linomp/acoustic-cam-usfq/development_version/postProc/16_mics_PSF.bmp

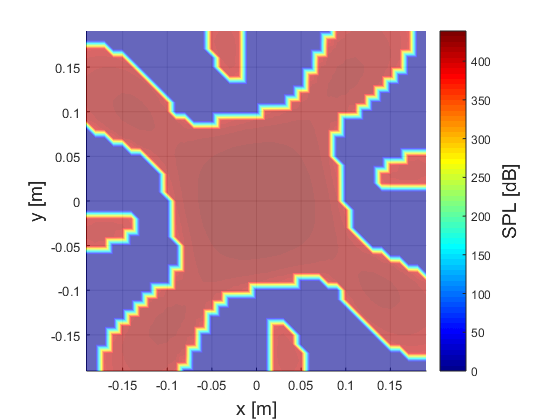
development_version/postProc/16_mics_PSF.bmp
