linomp/acoustic-cam-usfq/development_version/postProc/16_mics_PSF_w.bmp

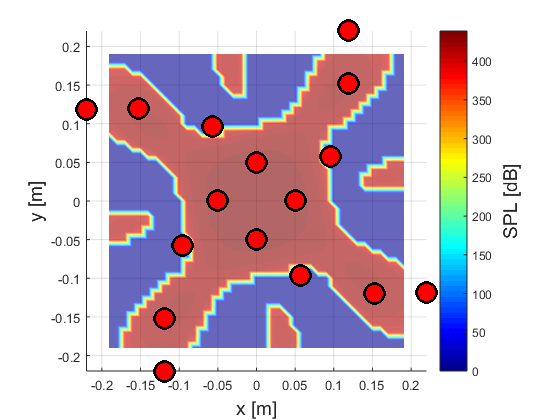
development_version/postProc/16_mics_PSF_w.bmp
