linomp/acoustic-cam-usfq/development_version/postProc/control_pt.bmp

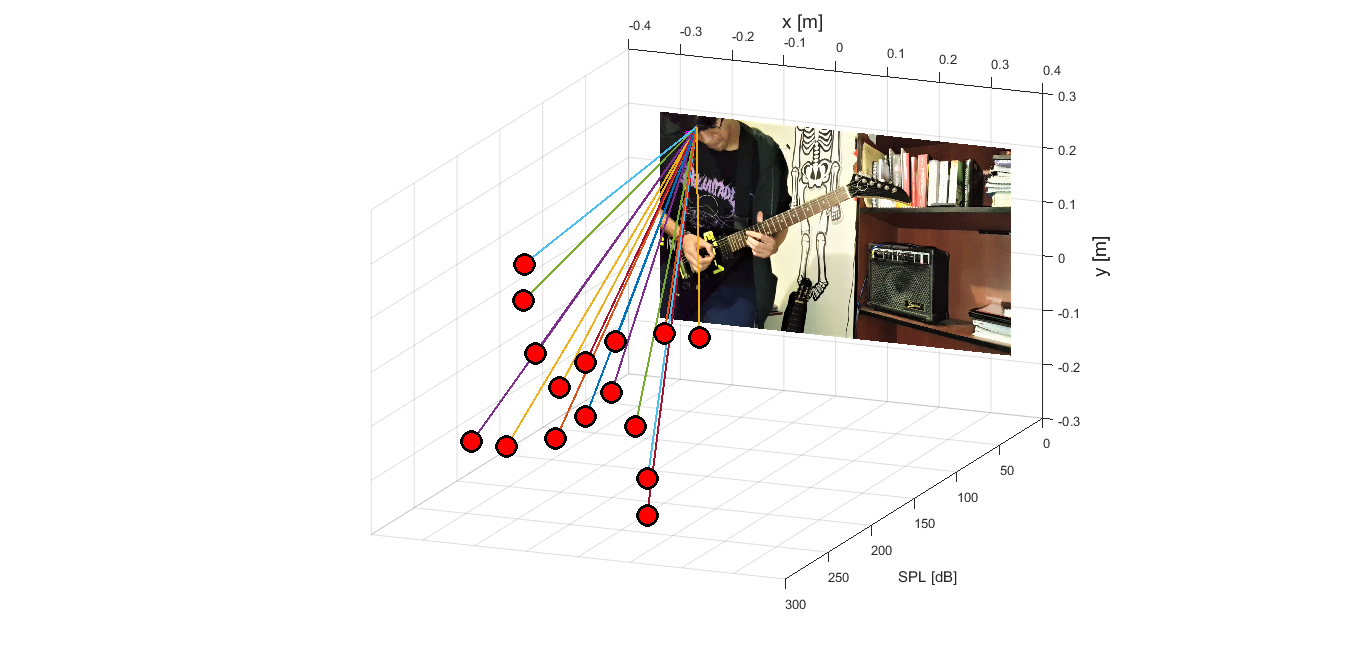
development_version/postProc/control_pt.bmp
