linomp/acoustic-cam-usfq/development_version/postProc/gtr2.png

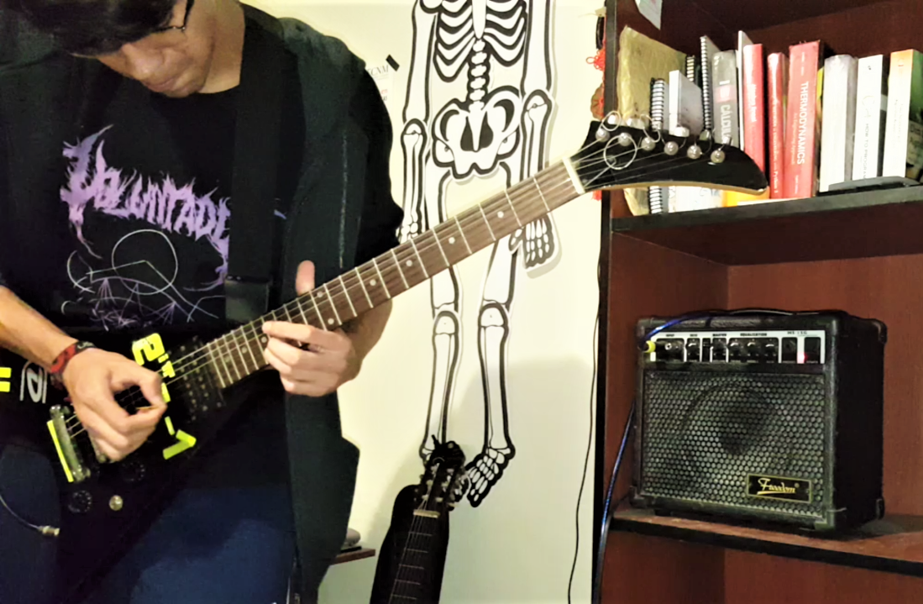
development_version/postProc/gtr2.png
