linomp/acoustic-cam-usfq/development_version/postProc/just_pic.bmp

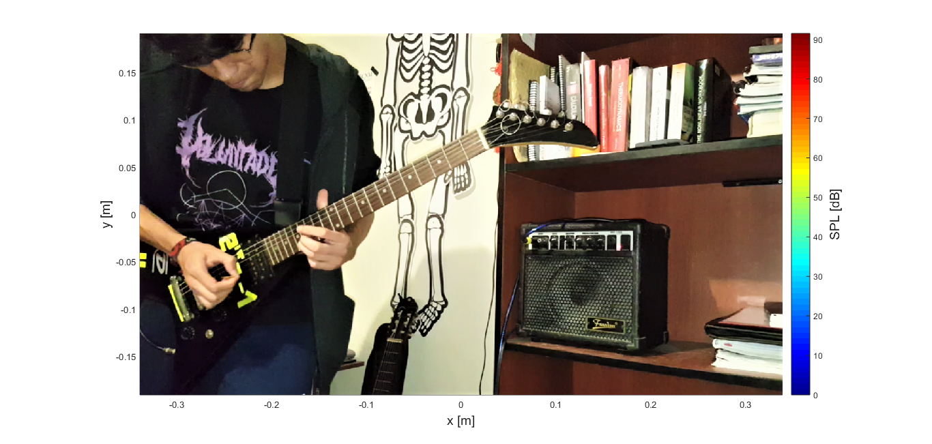
development_version/postProc/just_pic.bmp
