linomp/acoustic-cam-usfq/development_version/postProc/pic_n_mics.bmp

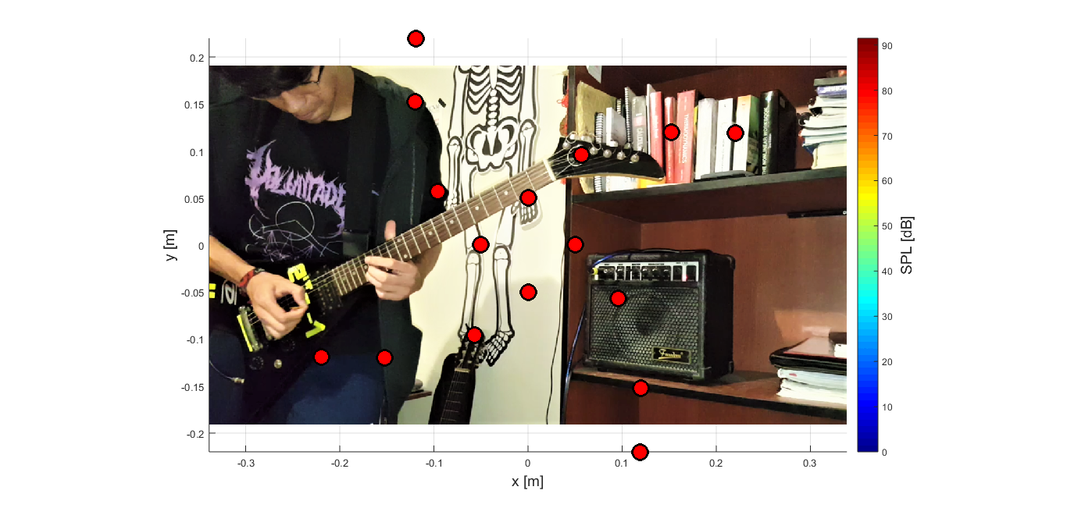
development_version/postProc/pic_n_mics.bmp
