linomp/acoustic-cam-usfq/development_version/postProc/uma_16_PSF.bmp

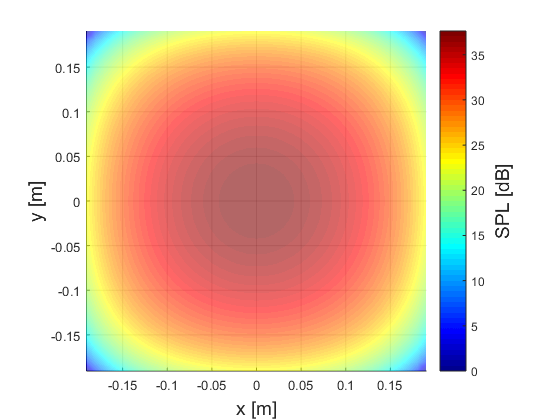
development_version/postProc/uma_16_PSF.bmp
