linomp/acoustic-cam-usfq/development_version/postProc/underbrink_16.bmp

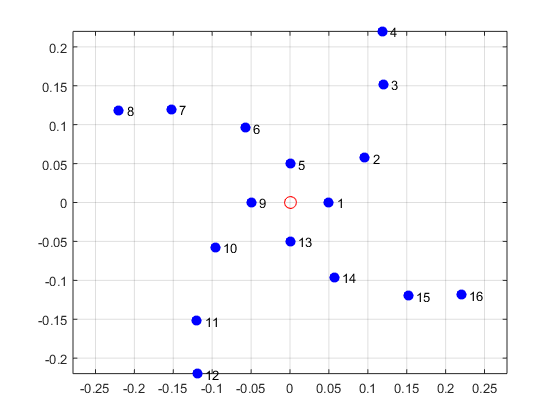
development_version/postProc/underbrink_16.bmp
