linomp/acoustic-cam-usfq/readme_img/process.PNG

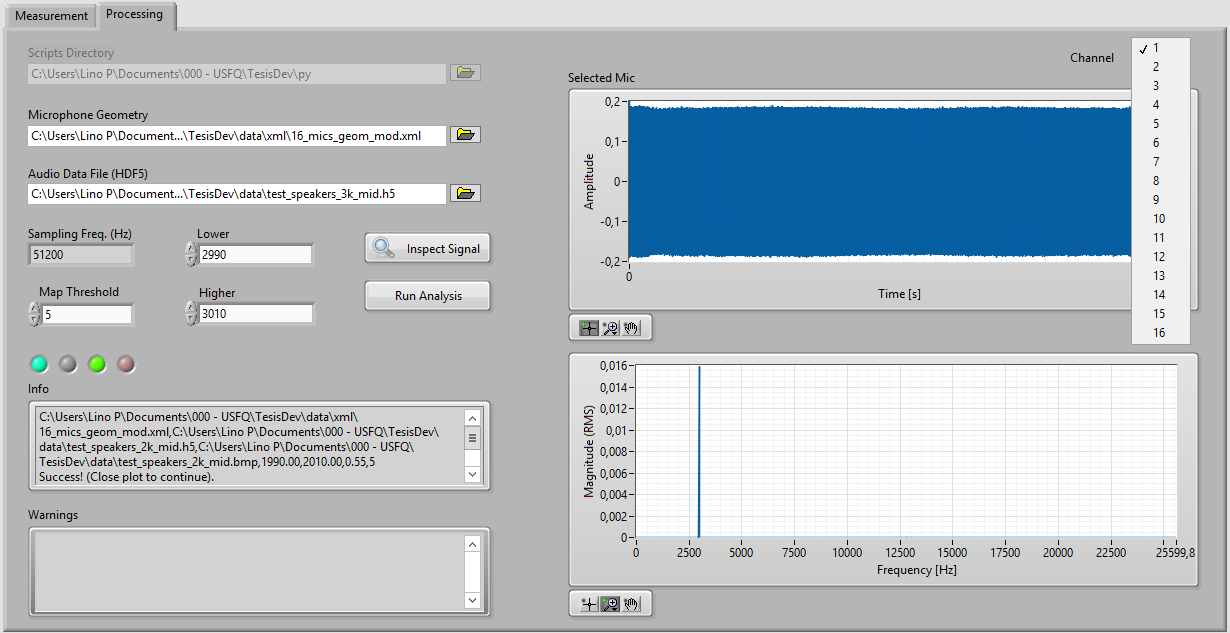
readme_img/process.PNG
