linomp/acoustic-cam-usfq/development_version/experiments/example_1.bmp

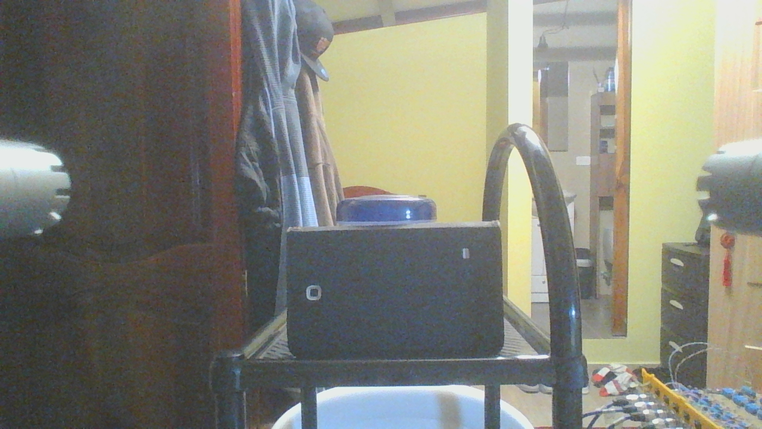
development_version/experiments/example_1.bmp
