linomp/acoustic-cam-usfq/development_version/postProc/result_3d.bmp

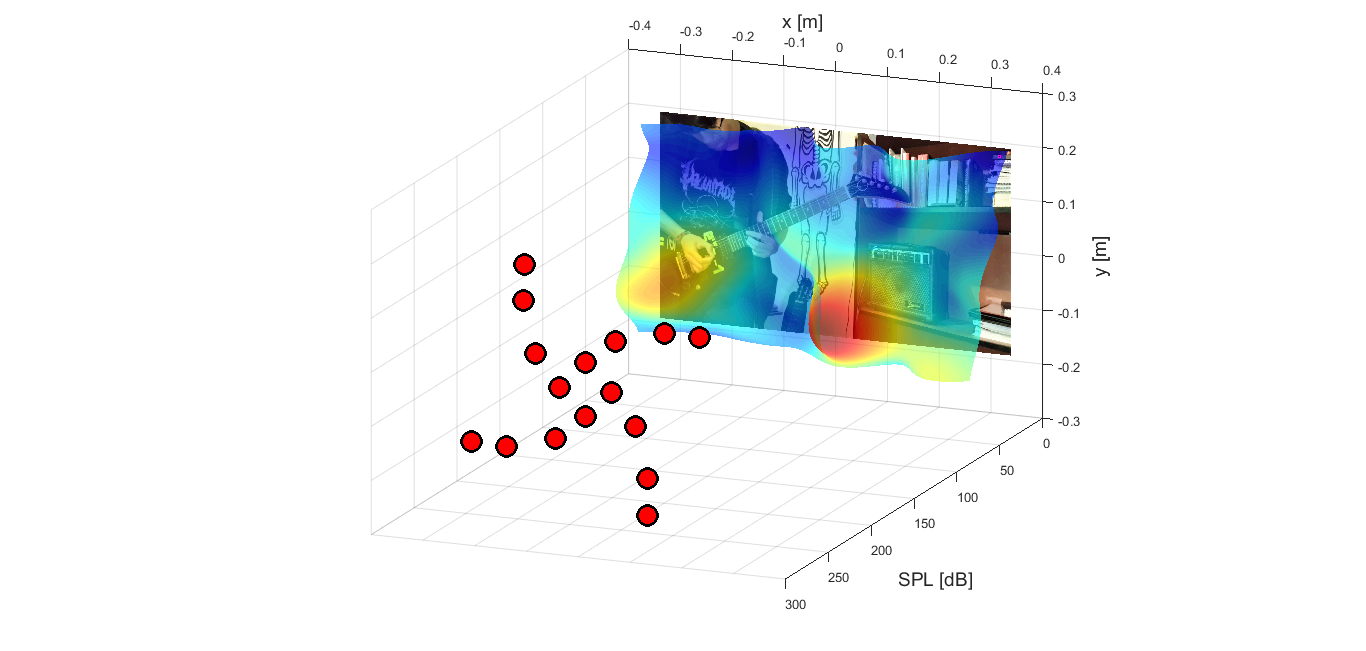
development_version/postProc/result_3d.bmp
