linomp/acoustic-cam-usfq/development_version/postProc/visualsTest.bmp

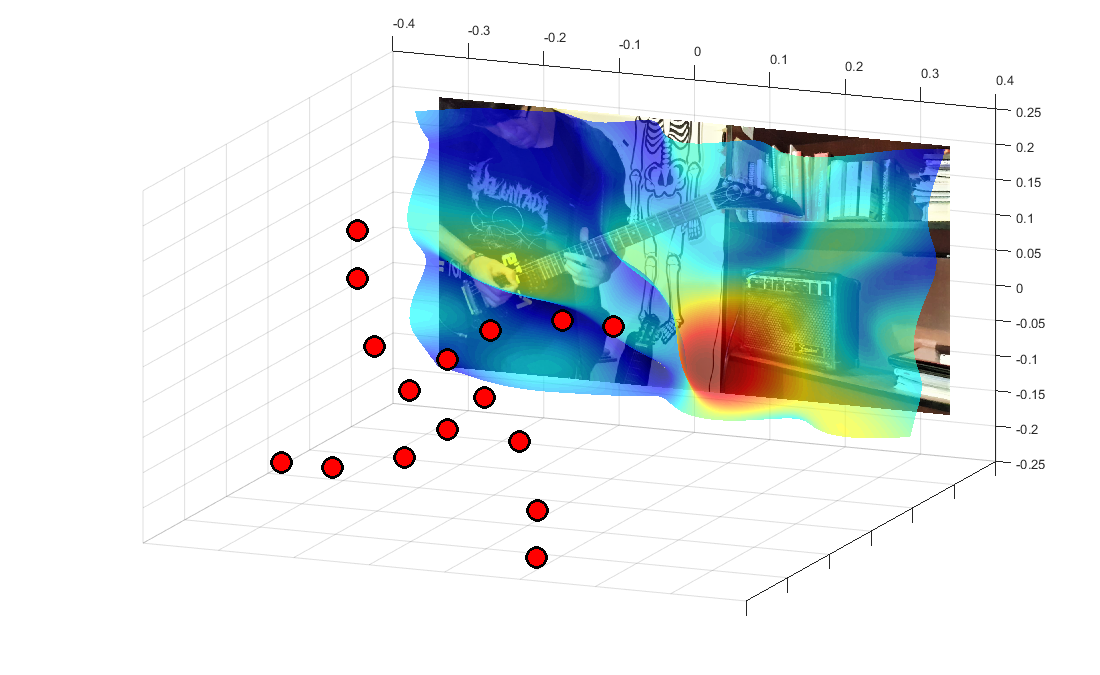
development_version/postProc/visualsTest.bmp
